schizobovine/pidplate/hardware/pidshield-mk-2.1.brd

## EAGLE design hardware/pidshield-mk-2.1.brd (2015-05-11)

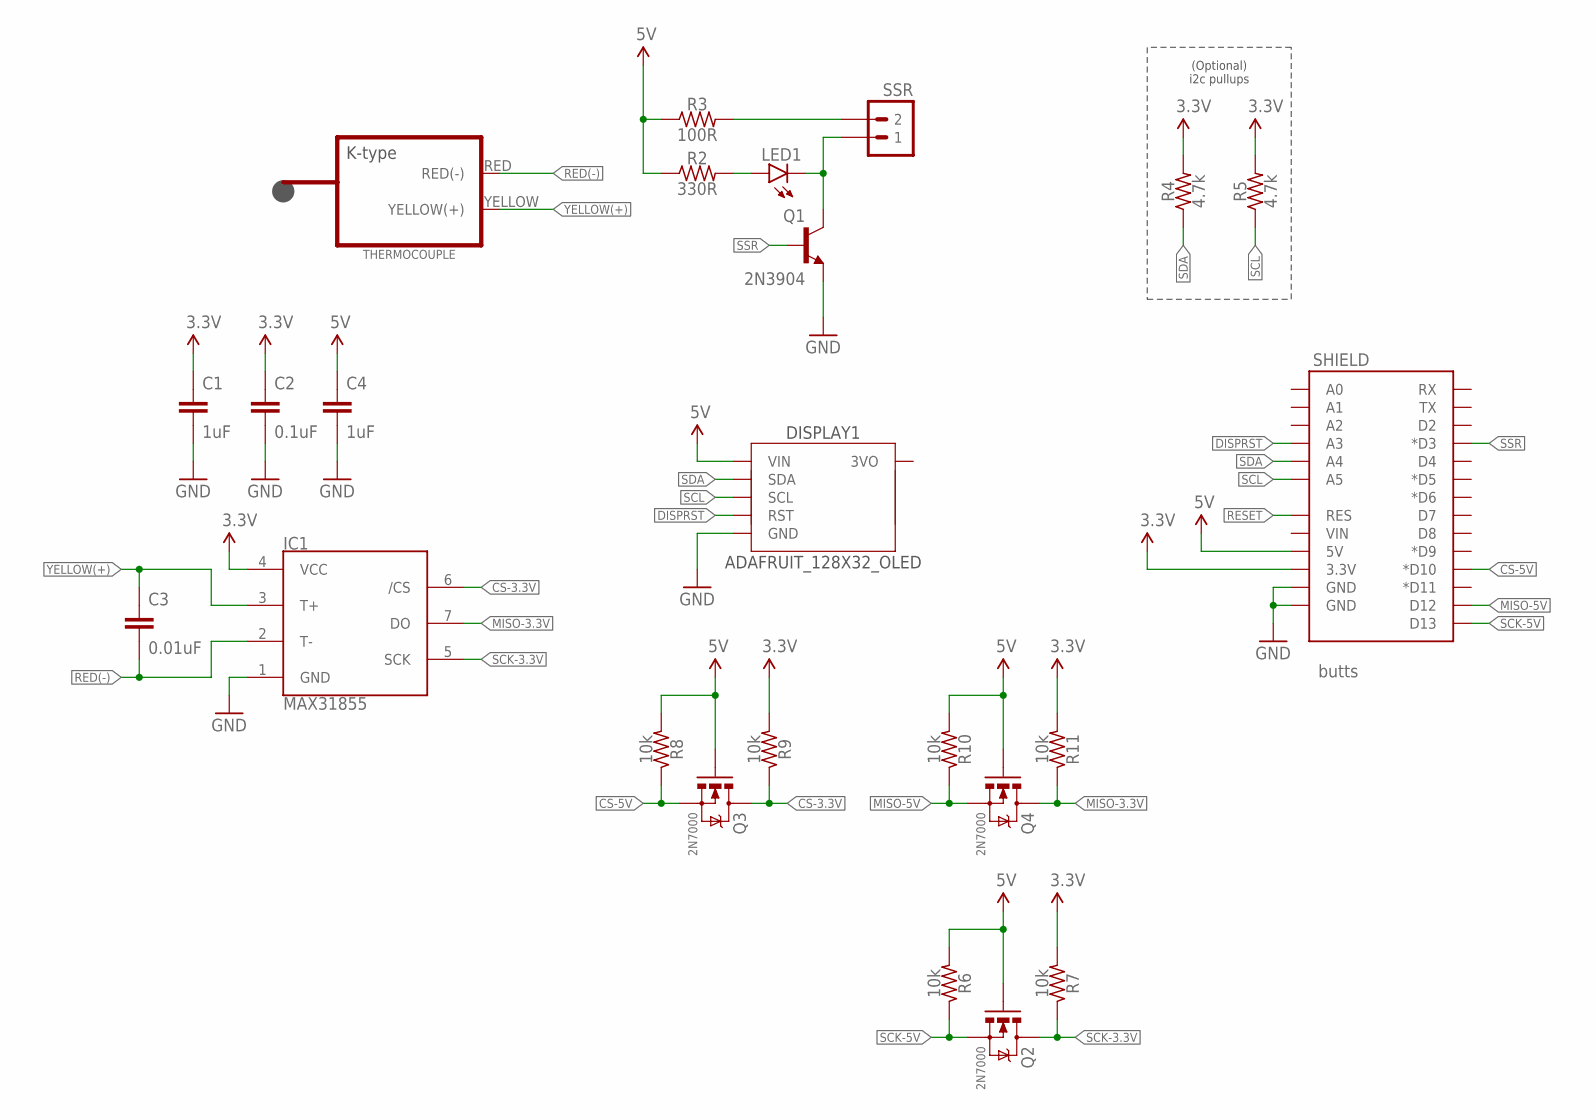
[picture p13: schematic pidshield-mk-2.1.sch]

Parts:
C1, C4: 1uF; C025-024X044
C2: 0.1uF; C025-024X044
C3: 0.01uF; C0805
DISPLAY1: ADAFRUIT_128X32_OLED; ADAFRUIT_128X32_OLED_I2C_CLOSER_NS
IC1: MAX31855; SOIC127P600X175-8N
LED1: LED3MM-LESS; LED3MM-LESSSILK
Q1: 2N3904; TO-92-AMMO
Q2, Q3, Q4: 2N7000; TO-92-AMMO
R2: 330R; RESISTOR-AXIAL-PTH-5.08MM
R3: 100R; RESISTOR-AXIAL-PTH-5.08MM
R4, R5: 4.7k; RESISTOR-AXIAL-PTH-5.08MM
R6, R7, R8, R9, R10, R11: 10k; RESISTOR-AXIAL-PTH-5.08MM
SHIELD: butts; ARDUINO_SHIELD_NOOUTLINE_INSIDE_SMALLER
SSR: M02JST-PTH-RA-SMALLPADS; JST-2-PH-RA-PTH-SMALLPADS
THERMOCOUPLE: THERMOCOUPLE-CONNECTORMINI-PCB; PCC-SMP

Connections:
3.3V: C1.1, C2.1, IC1.4 (VCC), R4.P$2 (2), R5.P$2 (2), R7.P$2 (2), R9.P$2 (2), R11.P$2 (2), SHIELD.3.3V
5V: C4.1, DISPLAY1.VIN, Q2.2 (G), Q3.2 (G), Q4.2 (G), R2.P$1 (1), R3.P$1 (1), R6.P$2 (2), R8.P$2 (2), R10.P$2 (2), SHIELD.5V
CS-3.3V: IC1.6 (/CS), Q3.3 (D), R9.P$1 (1)
CS-5V: Q3.1 (S), R8.P$1 (1), SHIELD.D10 (*D10)
DISPRST: DISPLAY1.RST, SHIELD.A3
GND: C1.2, C2.2, C4.2, DISPLAY1.GND, IC1.1 (GND), Q1.1 (E), SHIELD.GND@0 (GND), SHIELD.GND@1 (GND)
MISO-3.3V: IC1.7 (DO), Q4.3 (D), R11.P$1 (1)
MISO-5V: Q4.1 (S), R10.P$1 (1), SHIELD.D12
unnamed: LED1.A, R2.P$2 (2)
unnamed: LED1.K (C), Q1.3 (C), SSR.1
unnamed: R3.P$2 (2), SSR.2
RED(-): C3.2, IC1.2 (T-), THERMOCOUPLE.RED (RED(-))
RESET: SHIELD.RES
SCK-3.3V: IC1.5 (SCK), Q2.3 (D), R7.P$1 (1)
SCK-5V: Q2.1 (S), R6.P$1 (1), SHIELD.D13
SCL: DISPLAY1.SCL, R5.P$1 (1), SHIELD.A5
SDA: DISPLAY1.SDA, R4.P$1 (1), SHIELD.A4
SSR: Q1.2 (B), SHIELD.D3 (*D3)
YELLOW(+): C3.1, IC1.3 (T+), THERMOCOUPLE.YELLOW (YELLOW(+))

Notes on the sheet:
(Optional) i2c pullups

Board: 2 copper layers, 30 parts (2 on the bottom side), 18 nets, no tracks yet.

Other parts of the board:
U$2: COW
U$3: COW_SMALL
U$4, U$5: CC-BY-SA-4.0-NO-URL
U$6: OSHWLOGO_TOP_0.2_A
U$7: OSHWLOGO_BOT_0.2_A
