schizobovine/pidplate/hardware/pidshield-mk-2.brd

## EAGLE design hardware/pidshield-mk-2.brd (2014-12-28)

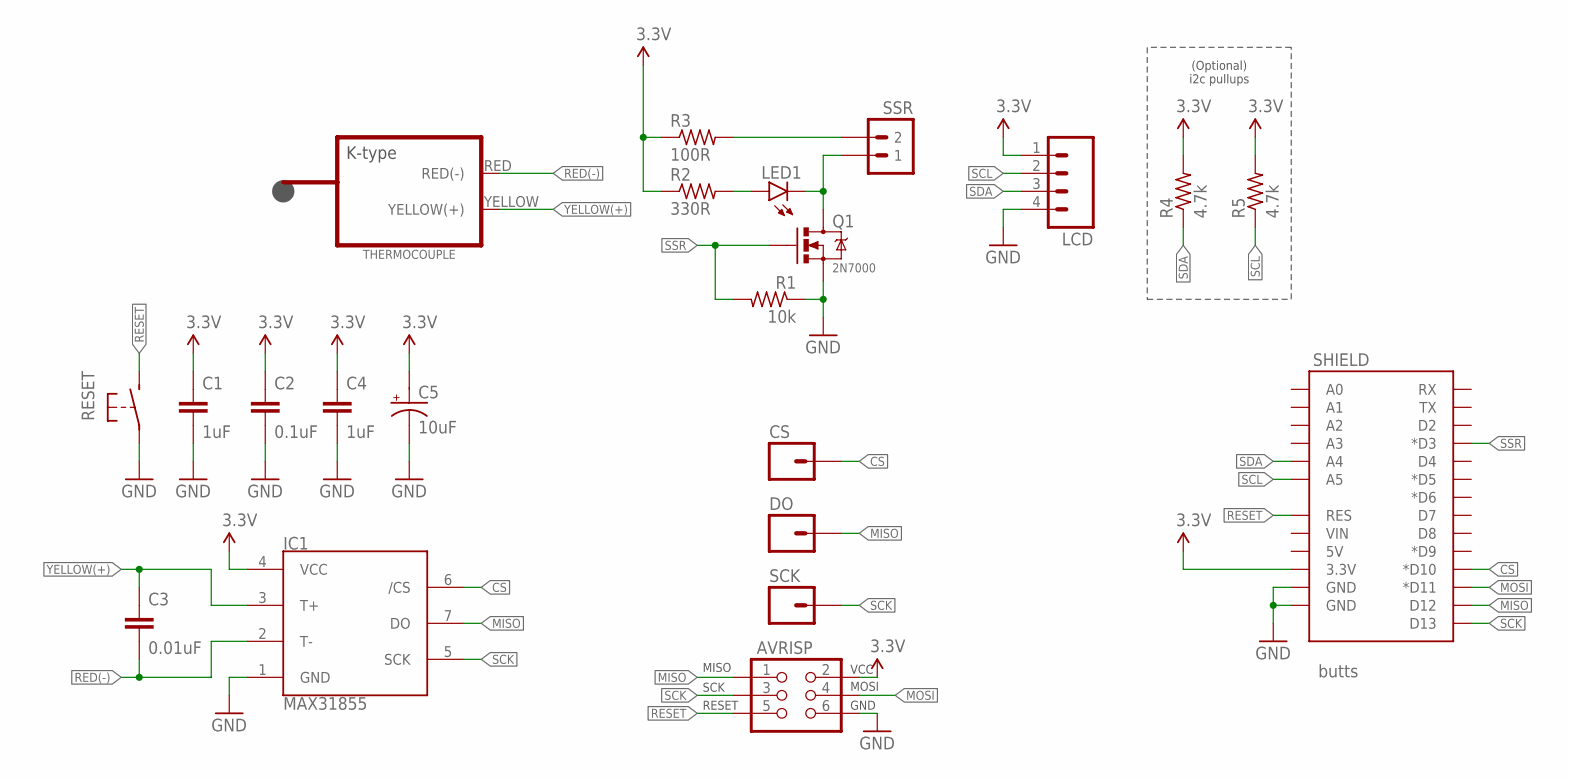
[picture p14: schematic pidshield-mk-2.sch]

Parts:
AVRISP: AVR_SPI_PRG_6PTH; 2X3
C1, C4: 1uF; C025-024X044
C2: 0.1uF; C025-024X044
C3: 0.01uF; C025-024X044
C5: 10uF; E2-5
CS: M01PTH; 1X01
DO: M01PTH; 1X01
IC1: MAX31855; SOIC127P600X175-8N
LCD: M04JST_XH_RA; JST-4-XH-RA-PTH
LED1: LED3MM
Q1: 2N7000; TO-92-AMMO
R1: 10k; RESISTOR-AXIAL-PTH-6.35MM
R2: 330R; RESISTOR-AXIAL-PTH-6.35MM
R3: 100R; RESISTOR-AXIAL-PTH-6.35MM
R4, R5: 4.7k; RESISTOR-AXIAL-PTH-6.35MM
RESET: SPST-NO-TACT6MM-PTH-SMALL-PADS; DTS-6-SMALL-PADS
SCK: M01PTH; 1X01
SHIELD: butts; ARDUINO_SHIELD_NOOUTLINE_INSIDE_SMALLER
SSR: M02JST-PTH-RA-SMALLPADS; JST-2-PH-RA-PTH-SMALLPADS
THERMOCOUPLE: THERMOCOUPLE-CONNECTORMINI-PCB; PCC-SMP

Connections:
3.3V: AVRISP.2 (VCC), C1.1, C2.1, C4.1, C5.+, IC1.4 (VCC), LCD.1, R2.P$1 (1), R3.P$1 (1), R4.P$2 (2), R5.P$2 (2), SHIELD.3.3V
CS: CS.1, IC1.6 (/CS), SHIELD.D10 (*D10)
GND: AVRISP.6 (GND), C1.2, C2.2, C4.2, C5.-, IC1.1 (GND), LCD.4, Q1.1 (S), R1.P$1 (1), RESET.1, RESET.2 (1), SHIELD.GND@0 (GND), SHIELD.GND@1 (GND)
MISO: AVRISP.1 (MISO), DO.1, IC1.7 (DO), SHIELD.D12
MOSI: AVRISP.4 (MOSI), SHIELD.D11 (*D11)
unnamed: LED1.A, R2.P$2 (2)
unnamed: LED1.K (C), Q1.3 (D), SSR.1
unnamed: R3.P$2 (2), SSR.2
RED(-): C3.2, IC1.2 (T-), THERMOCOUPLE.RED (RED(-))
RESET: AVRISP.5 (RESET), RESET.3 (2), RESET.4 (2), SHIELD.RES
SCK: AVRISP.3 (SCK), IC1.5 (SCK), SCK.1, SHIELD.D13
SCL: LCD.2, R5.P$1 (1), SHIELD.A5
SDA: LCD.3, R4.P$1 (1), SHIELD.A4
SSR: Q1.2 (G), R1.P$2 (2), SHIELD.D3 (*D3)
YELLOW(+): C3.1, IC1.3 (T+), THERMOCOUPLE.YELLOW (YELLOW(+))

Notes on the sheet:
(Optional) i2c pullups
