schizobovine/pidplate/hardware/pidshield-mk-2.brd

## EAGLE design hardware/pidshield-mk-2.brd (continued)

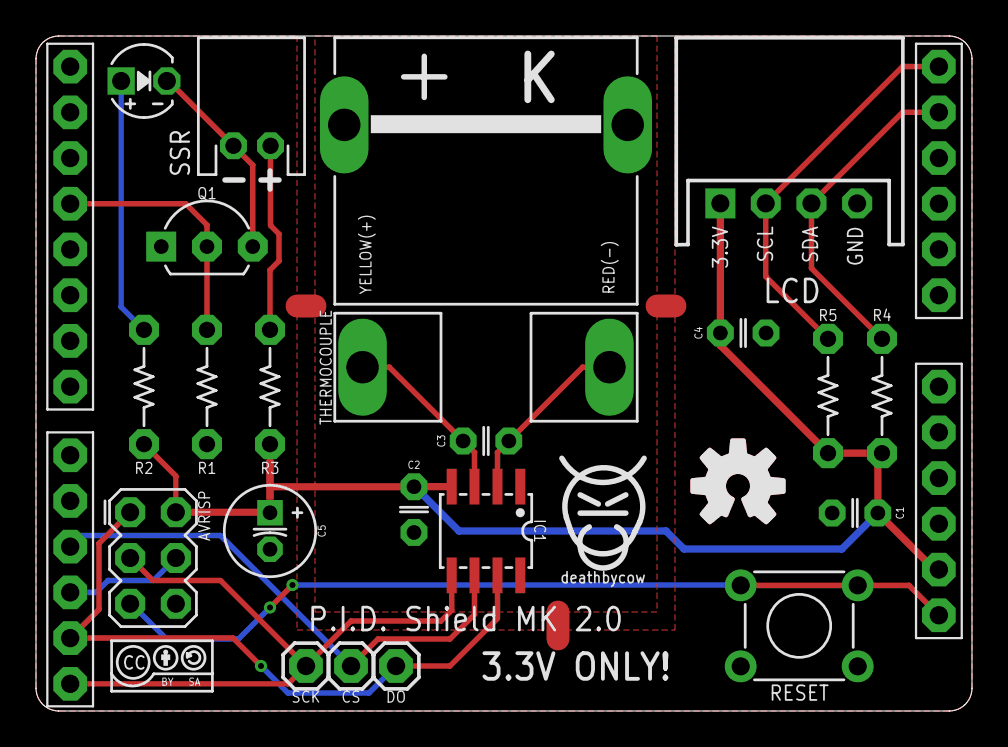
[picture p15: board pidshield-mk-2.brd from above]

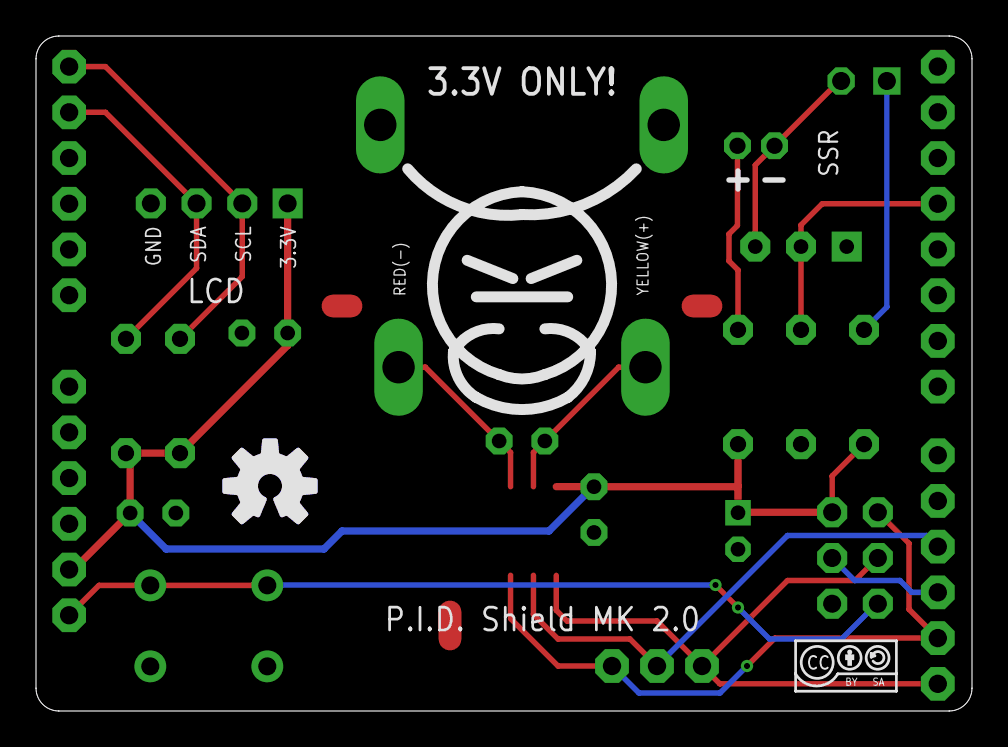
[picture p16: board pidshield-mk-2.brd from below]

Board: 2 copper layers, 52.0 x 37.5 mm, 28 parts (2 on the bottom side), 15 nets.

Other parts of the board:
U$2: COW
U$3: COW_SMALL
U$4, U$5: CC-BY-SA-4.0-NO-URL
U$6: OSHWLOGO_TOP_0.2_A
U$7: OSHWLOGO_BOT_0.2_A
