schizobovine/pidplate/hardware/pidshield-mk-1.brd

## EAGLE design hardware/pidshield-mk-1.brd (2014-12-15)

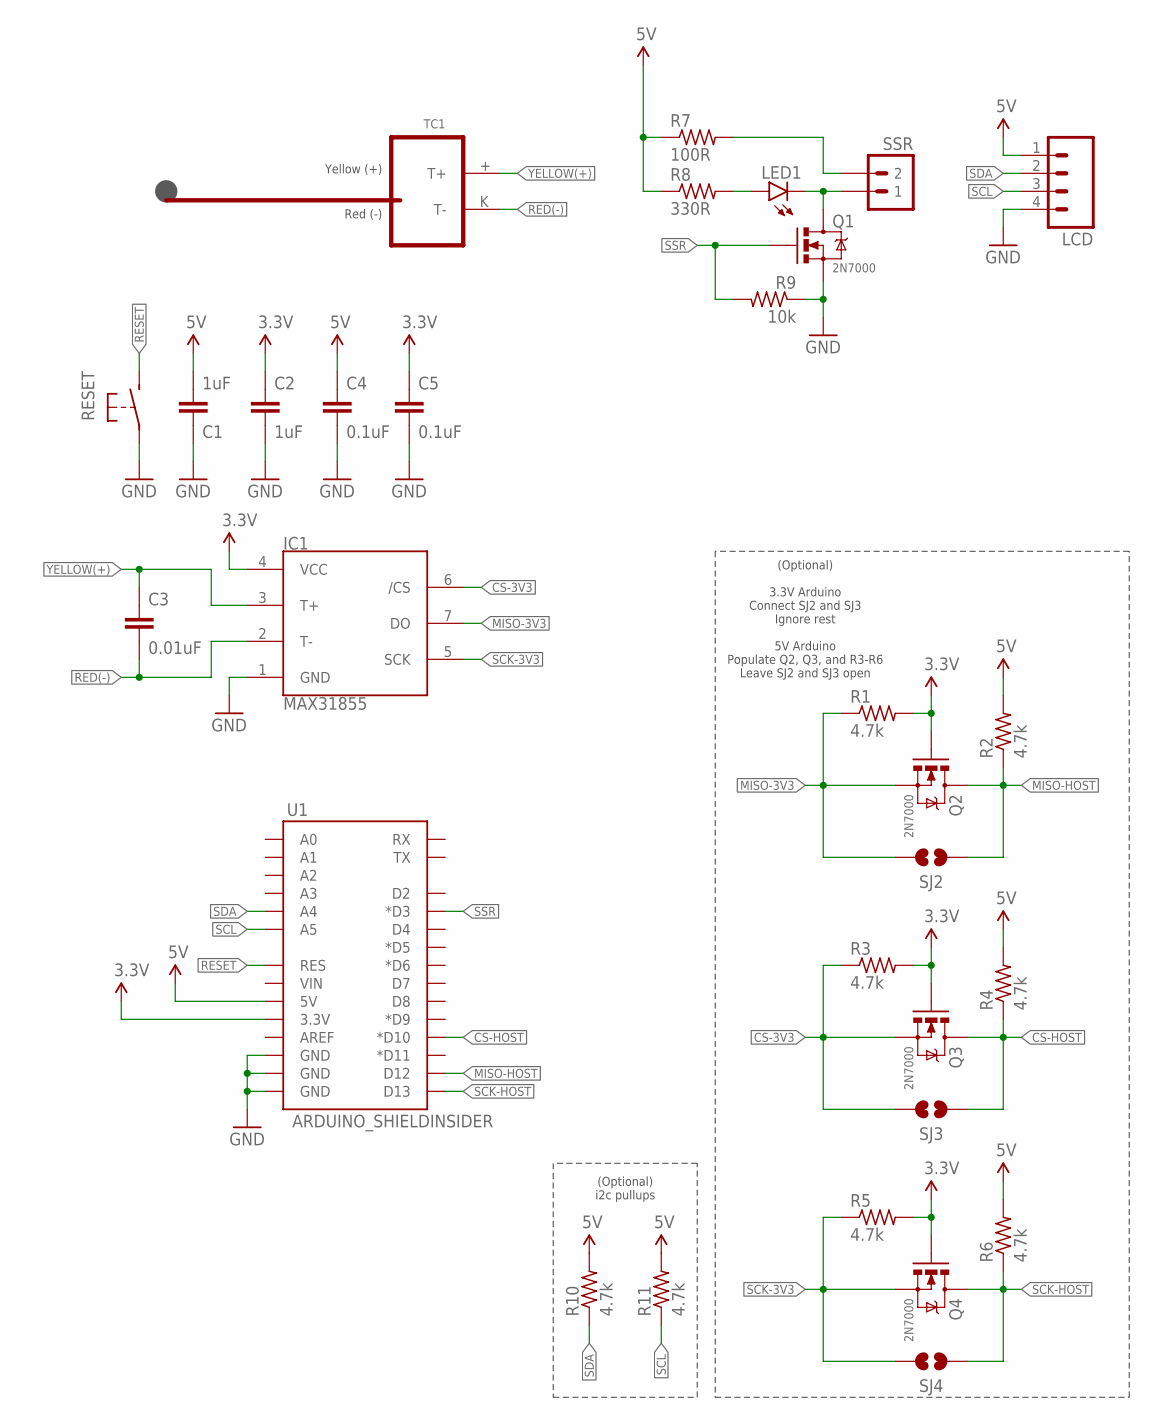
[picture p17: schematic pidshield-mk-1.sch]

Parts:
C1, C2: 1uF; C025-024X044
C3: 0.01uF; C025-024X044
C4, C5: 0.1uF; C025-024X044
IC1: MAX31855; SOIC127P600X175-8N
LCD: M04JST_XH_RA; JST-4-XH-RA-PTH
LED1: LED3MM
Q1, Q2, Q3, Q4: 2N7000; TO-92-AMMO
R1, R2, R3, R4, R5, R6, R10, R11: 4.7k; RESISTOR-AXIAL-PTH-6.35MM
R7: 100R; RESISTOR-AXIAL-PTH-6.35MM
R8: 330R; RESISTOR-AXIAL-PTH-6.35MM
R9: 10k; RESISTOR-AXIAL-PTH-6.35MM
RESET: SPST-NO-TACT3MM-RA; TACTILE-PTH-SIDE
SJ2, SJ3, SJ4: JUMPER-PAD-2-NOYES_SILK; PAD-JUMPER-2-NO_YES_SILK
SSR: M02JST-PTH-RA-SMALLPADS; JST-2-PH-RA-PTH-SMALLPADS
TC1: PCC-SMP-K; PCC-SMP
U1: ARDUINO_SHIELDINSIDER; ARDUINO_SHIELD_NOOUTLINE_INSIDE

Connections:
3.3V: C2.1, C5.1, IC1.4 (VCC), Q2.2 (G), Q3.2 (G), Q4.2 (G), R1.P$2 (2), R3.P$2 (2), R5.P$2 (2), U1.3.3V
5V: C1.2, C4.1, LCD.1, R2.P$2 (2), R4.P$2 (2), R6.P$2 (2), R7.P$1 (1), R8.P$1 (1), R10.P$2 (2), R11.P$2 (2), U1.5V
CS-3V3: IC1.6 (/CS), Q3.1 (S), R3.P$1 (1), SJ3.2
CS-HOST: Q3.3 (D), R4.P$1 (1), SJ3.1, U1.D10 (*D10)
GND: C1.1, C2.2, C4.2, C5.2, IC1.1 (GND), LCD.4, Q1.1 (S), R9.P$1 (1), RESET.1, U1.GND@0 (GND), U1.GND@1 (GND), U1.GND@2 (GND)
MISO-3V3: IC1.7 (DO), Q2.1 (S), R1.P$1 (1), SJ2.2
MISO-HOST: Q2.3 (D), R2.P$1 (1), SJ2.1, U1.D12
unnamed: LED1.A, R8.P$2 (2)
unnamed: LED1.K (C), Q1.3 (D), SSR.1
unnamed: R7.P$2 (2), SSR.2
RED(-): C3.2, IC1.2 (T-), TC1.K (T-)
RESET: RESET.2, U1.RES
SCK-3V3: IC1.5 (SCK), Q4.1 (S), R5.P$1 (1), SJ4.2
SCK-HOST: Q4.3 (D), R6.P$1 (1), SJ4.1, U1.D13
SCL: LCD.3, R11.P$1 (1), U1.A5
SDA: LCD.2, R10.P$1 (1), U1.A4
SSR: Q1.2 (G), R9.P$2 (2), U1.D3 (*D3)
YELLOW(+): C3.1, IC1.3 (T+), TC1.+ (T+)

Notes on the sheet:
(Optional) 3.3V Arduino Connect SJ2 and SJ3 Ignore rest 5V Arduino Populate Q2, Q3, and R3-R6 Leave SJ2 and SJ3 open
(Optional) i2c pullups

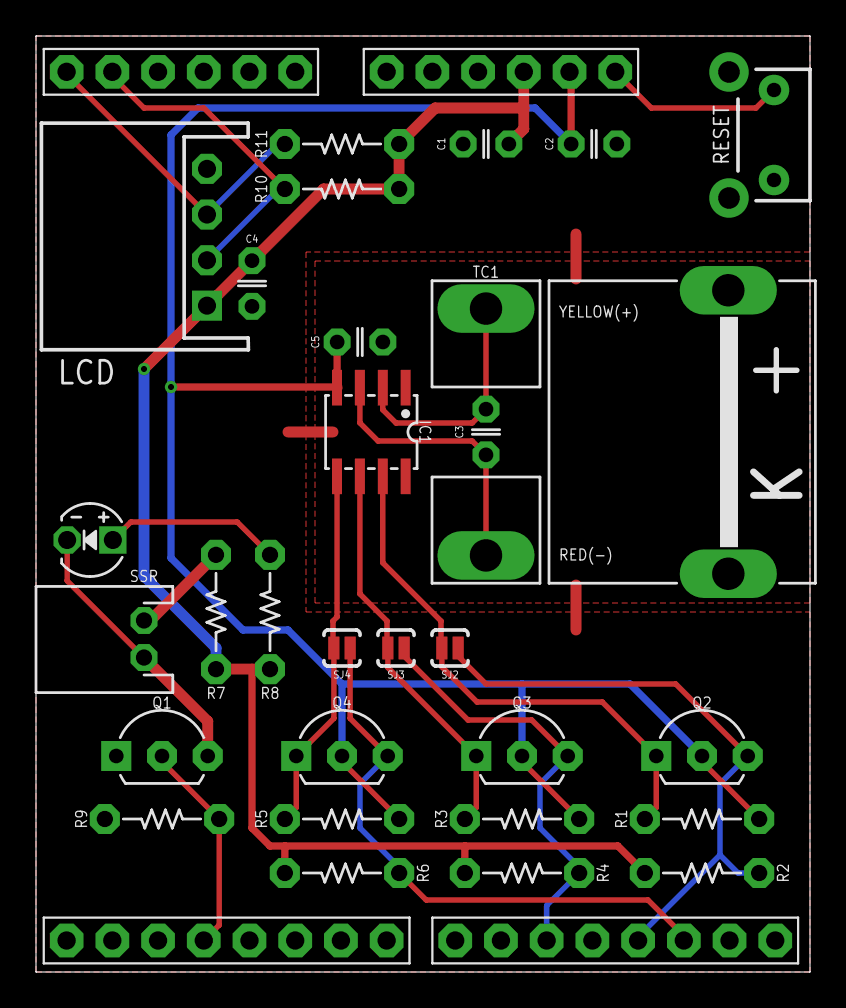
[picture p18: board pidshield-mk-1.brd from above]

Board: 2 copper layers, 43.0 x 52.0 mm, 30 parts (0 on the bottom side), 18 nets.
