schizobovine/pidplate/hardware/pidplate-mk-2.1.brd

## EAGLE design hardware/pidplate-mk-2.1.brd (2014-12-15)

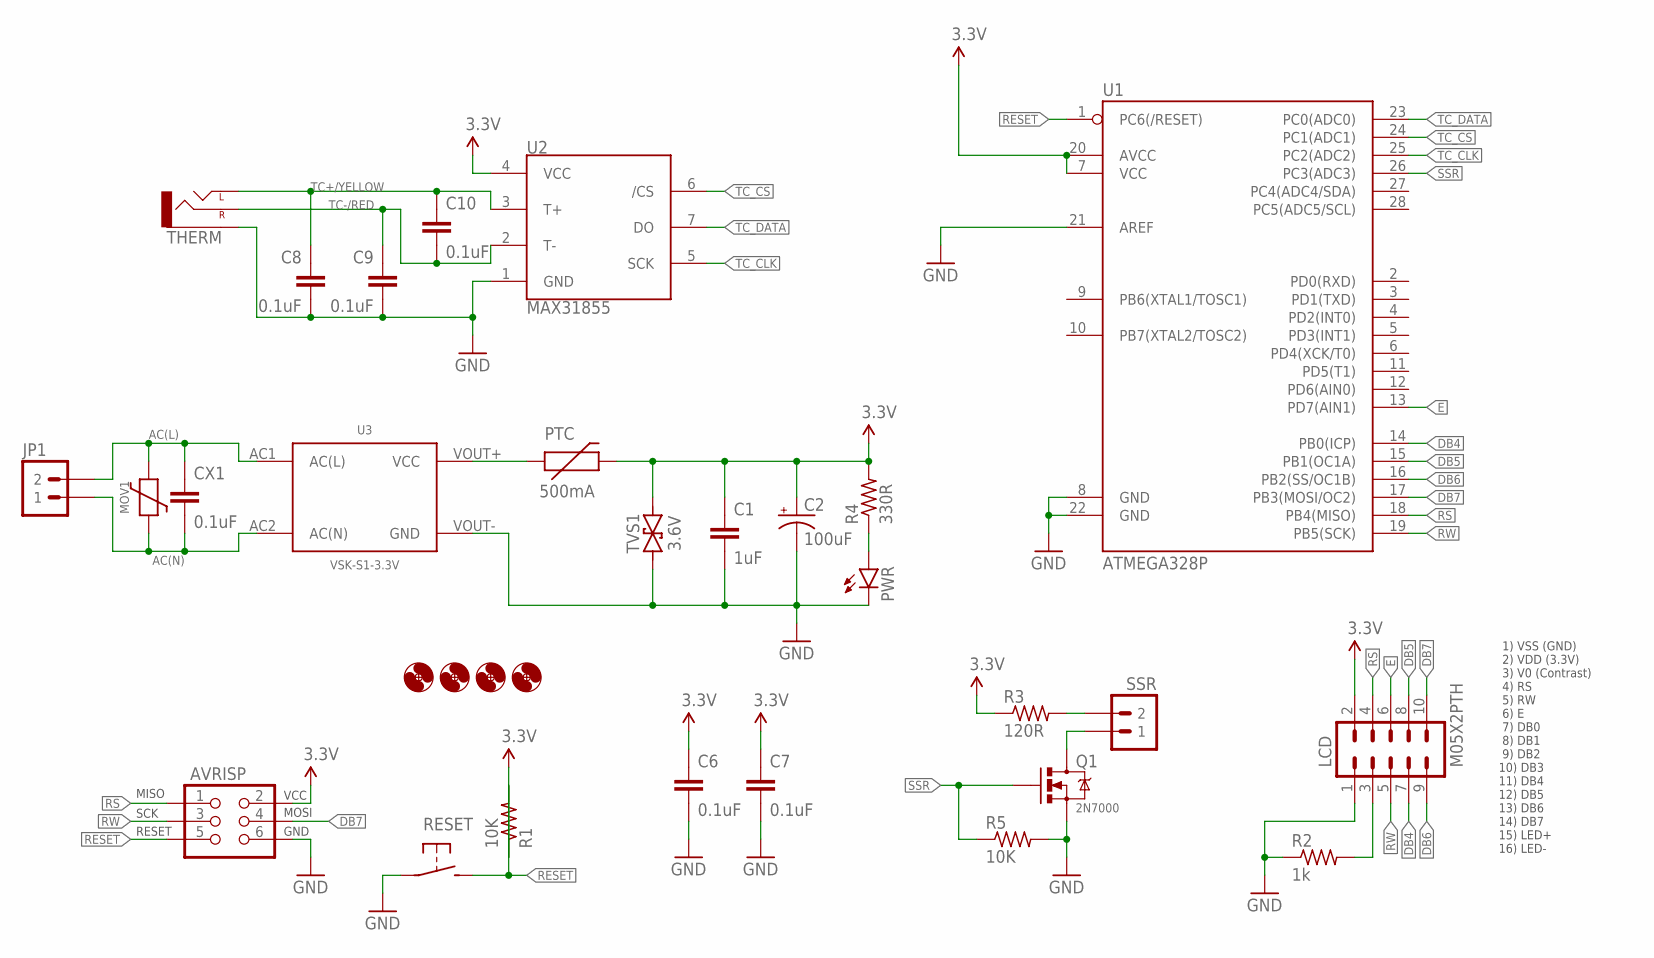
[picture p19: schematic pidplate-mk-2.1.sch]

Parts:
AVRISP: AVR_SPI_PRG_6PTH; 2X3
C1: 1uF; C025-024X044
C2: 100uF; E2,5-7
C6, C7, C8, C9, C10: 0.1uF; C025-024X044
CX1: 0.1uF; XC10B5
H1, H2, H3, H4: HOLE#2; HOLE-#2
JP1: M023.5MM; SCREWTERMINAL-3.5MM-2
LCD: M05X2PTH; AVR_ICSP
MOV1: VARISITORVAR-5.08MM-PTH; VAR-5.08MM-PTH
PTC: 500mA; PTC
PWR: LED3MM
Q1: 2N7000; TO-92-AMMO
R1, R5: 10K; RESISTOR-AXIAL-PTH-6.35MM
R2: 1k; RESISTOR-AXIAL-PTH-6.35MM
R3: 120R; RESISTOR-AXIAL-PTH-6.35MM
R4: 330R; RESISTOR-AXIAL-PTH-6.35MM
RESET: SPST-NO-TACT3MM-PTH-SMALL-PADS; DTS-3-SMALL-PADS
SSR: M02JST-PTH-VERT; JST-2-PH-VERT-PTH
THERM: AUDIO-JACK2.5MM; STEREOJACK2.5MM_STEREOJACK2.5MM
TVS1: 3.6V; DO-41-TVS
U1: ATMEGA328P; DIL28-3
U2: MAX31855; SOIC127P600X175-8N
U3: VSK-S1-3.3V; VSK-S1

Connections:
3.3V: AVRISP.2 (VCC), C1.1, C2.+, C6.1, C7.1, LCD.2, PTC.P$2 (2), R1.P$1 (1), R3.P$1 (1), R4.P$2 (2), TVS1.P$2 (2), U1.7 (VCC), U1.20 (AVCC), U2.4 (VCC)
AC(L): CX1.1, JP1.2, MOV1.2, U3.AC1 (AC(L))
AC(N): CX1.2, JP1.1, MOV1.1, U3.AC2 (AC(N))
DB4: LCD.7, U1.14 (PB0(ICP))
DB5: LCD.8, U1.15 (PB1(OC1A))
DB6: LCD.9, U1.16 (PB2(SS/OC1B))
DB7: AVRISP.4 (MOSI), LCD.10, U1.17 (PB3(MOSI/OC2))
E: LCD.6, U1.13 (PD7(AIN1))
GND: AVRISP.6 (GND), C1.2, C2.-, C6.2, C7.2, C8.2, C9.2, LCD.1, PWR.K (C), Q1.1 (S), R2.P$1 (1), R5.P$2 (2), RESET.1, THERM.SHIELD (SLEEVE), TVS1.P$1 (1), U1.8 (GND), U1.21 (AREF), U1.22 (GND), U2.1 (GND), U3.VOUT- (GND)
unnamed: PTC.P$1 (1), U3.VOUT+ (VCC)
unnamed: LCD.3, R2.P$2 (2)
unnamed: R3.P$2 (2), SSR.2
unnamed: Q1.3 (D), SSR.1
unnamed: PWR.A, R4.P$1 (1)
RESET: AVRISP.5 (RESET), R1.P$2 (2), RESET.2, U1.1 (PC6(/RESET))
RS: AVRISP.1 (MISO), LCD.4, U1.18 (PB4(MISO))
RW: AVRISP.3 (SCK), LCD.5, U1.19 (PB5(SCK))
SSR: Q1.2 (G), R5.P$1 (1), U1.26 (PC3(ADC3))
TC+/YELLOW: C8.1, C10.1, THERM.RING1 (LEFT), THERM.RING2 (LEFT), U2.3 (T+)
TC-/RED: C9.1, C10.2, THERM.TIP (RIGHT), U2.2 (T-)
TC_CLK: U1.25 (PC2(ADC2)), U2.5 (SCK)
TC_CS: U1.24 (PC1(ADC1)), U2.6 (/CS)
TC_DATA: U1.23 (PC0(ADC0)), U2.7 (DO)

Notes on the sheet:
1) VSS (GND) 2) VDD (3.3V) 3) V0 (Contrast) 4) RS 5) RW 6) E 7) DB0 8) DB1 9) DB2 10) DB3 11) DB4 12) DB5 13) DB6 14) DB7 15) LED+ 16) LED-

Board: 2 copper layers, 35 parts (2 on the bottom side), 23 nets, no tracks yet.

Other parts of the board:
U$1, U$4: OSHWLOGO_BOT_0.2
U$2, U$3: CC-BY-SA-4.0-NO-URL
