schizobovine/pidplate/hardware/pidplate-mk-2.brd

## EAGLE design hardware/pidplate-mk-2.brd (2014-12-11)

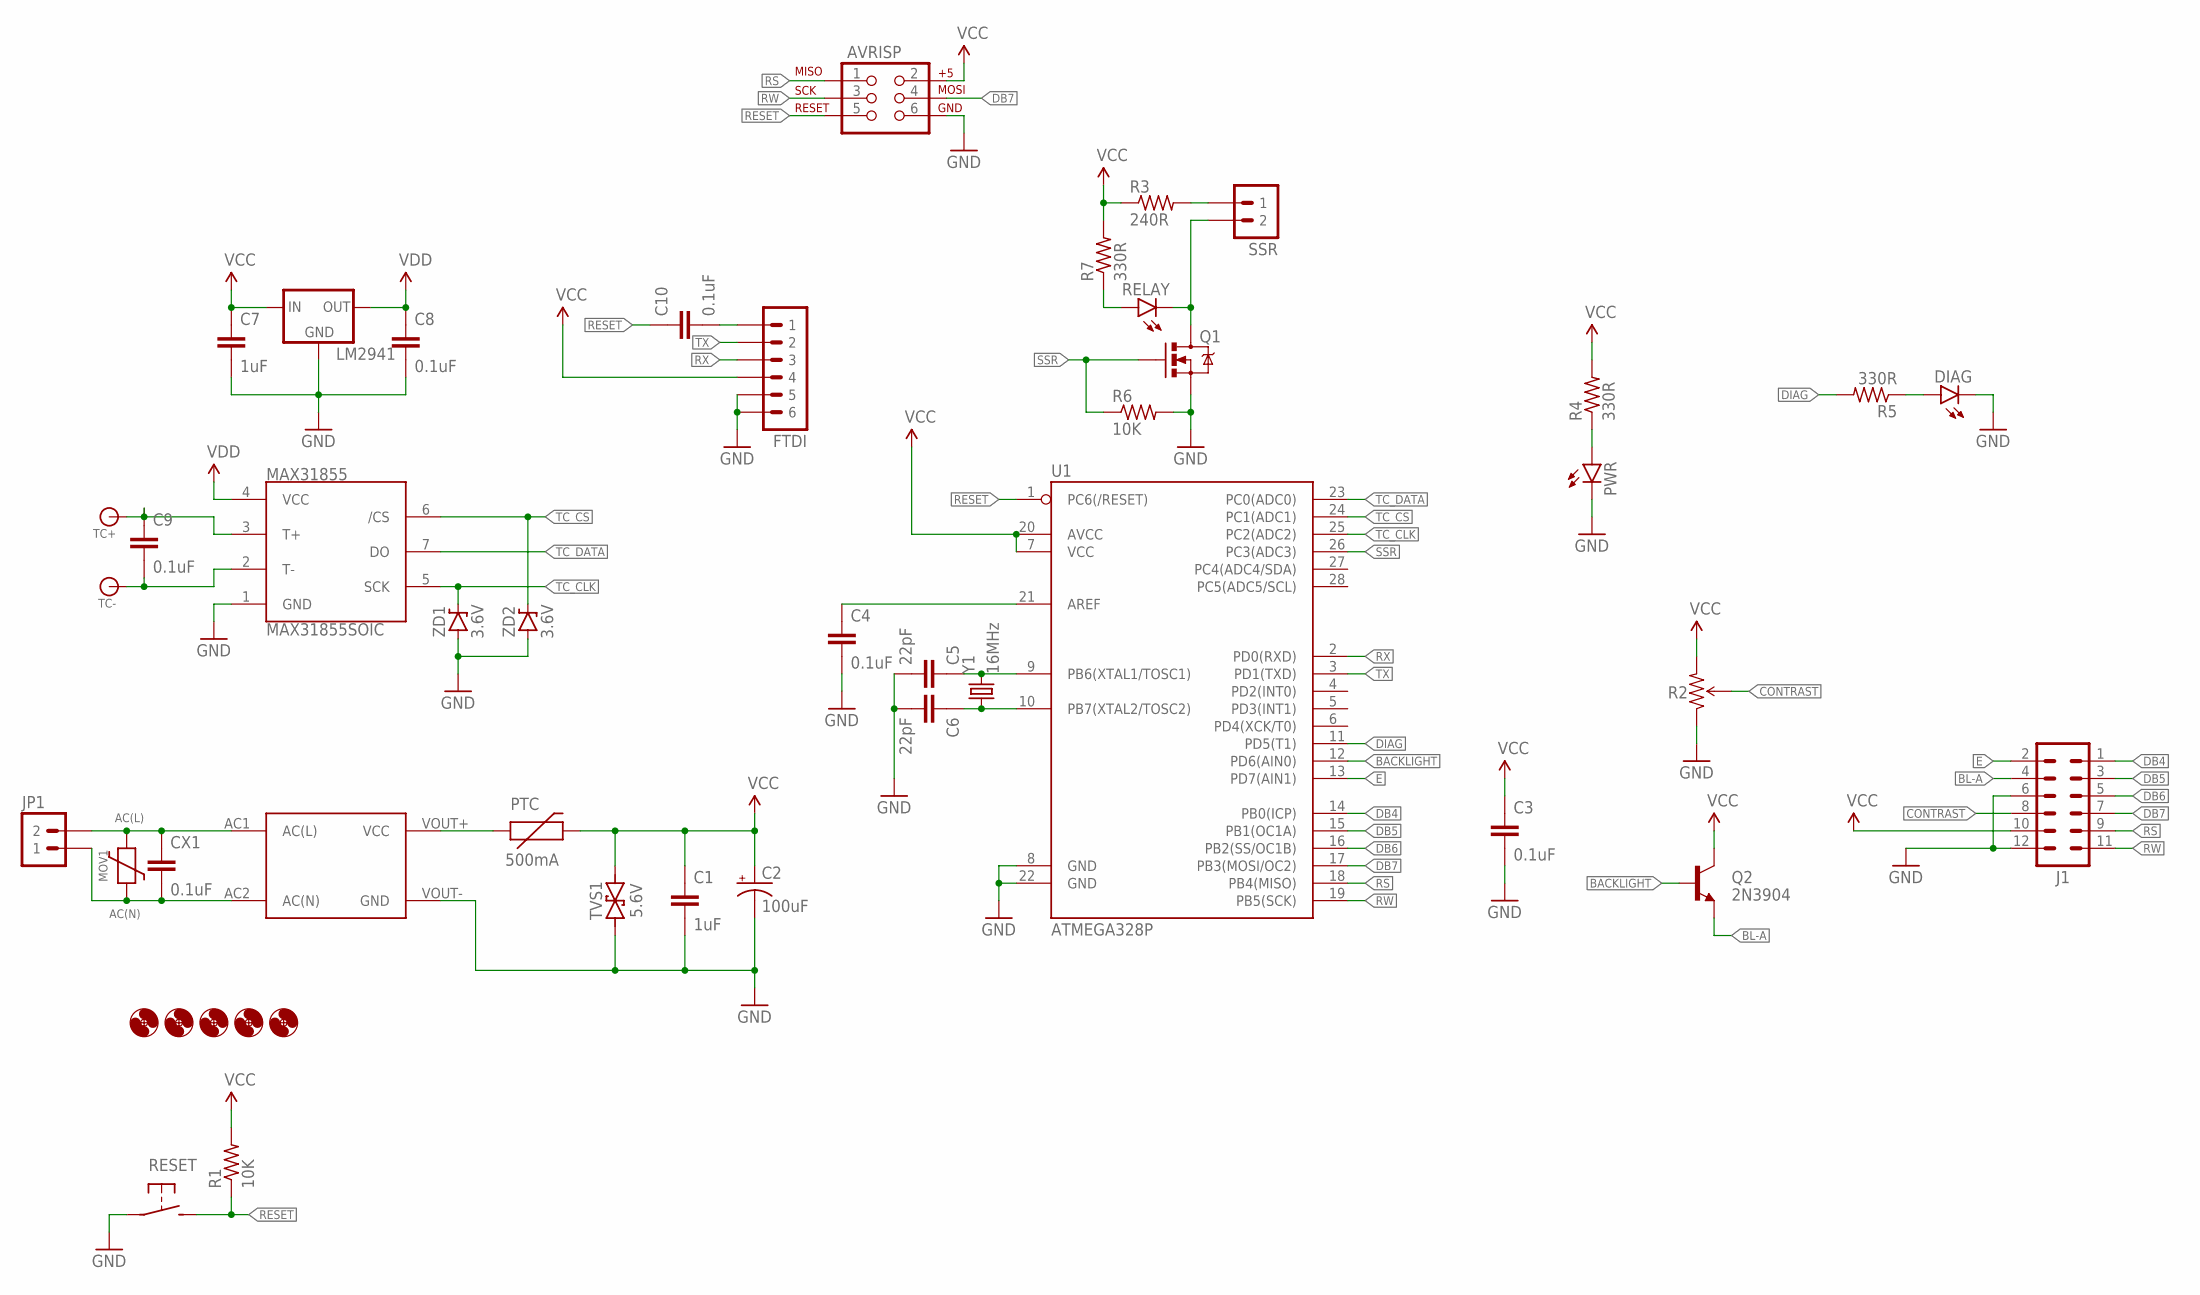
[picture p20: schematic pidplate-mk-2.sch]

Parts:
AVRISP: AVR_SPI_PRG_6PTH; 2X3
C1, C7: 1uF; C025-024X044
C2: 100uF; E2,5-7
C3, C4, C8, C9, C10: 0.1uF; C025-024X044
C5, C6: 22pF; C025-024X044
CX1: 0.1uF; XC10B5
DIAG: LED3MM
FTDI: M06SIP; 1X06
H1, H2, H3, H4, H5: HOLE#2; HOLE-#2
J1: M06X2PTH; 2X6_PTH
JP1: M023.5MM; SCREWTERMINAL-3.5MM-2
LM2941: L2941; TO-92-AMMO
MAX31855: MAX31855SOIC; SOIC127P600X175-8N
MOV1: VARISITORVAR-5.08MM-PTH; VAR-5.08MM-PTH
PTC: 500mA; PTC
PWR: LED3MM
Q1: 2N7000; TO-92-AMMO
Q2: 2N3904; TO-92-AMMO
R1: 10K; RESISTOR-AXIAL-PTH-5.08MM
R2: 20K; TRIM_POT_PTH
R3: 240R; RESISTOR-AXIAL-PTH-6.35MM
R4, R5, R7: 330R; RESISTOR-AXIAL-PTH-5.08MM
R6: 10K; RESISTOR-AXIAL-PTH-6.35MM
RELAY: LED3MM
RESET: SPST-NO-TACT3MM-RA; TACTILE-PTH-SIDE
SSR: M02JST-PTH-VERT; JST-2-PH-VERT-PTH
TC+: BANANA_CONNPTH-RA; BANANA-PTH-RA-SAFEWORD
TC-: BANANA_CONNPTH-RA; BANANA-PTH-RA-SAFEWORD
TVS1: 5.6V; DO-41-TVS
U1: ATMEGA328P; DIL28-3
U3: VSK-S1
Y1: 16MHz; HC49U-V
ZD1, ZD2: 3.6V; DIODE-7.68MM

Connections:
AC(L): CX1.1, JP1.2, MOV1.2, U3.AC1 (AC(L))
AC(N): CX1.2, JP1.1, MOV1.1, U3.AC2 (AC(N))
BACKLIGHT: Q2.2 (B), U1.12 (PD6(AIN0))
BL-A: J1.4, Q2.3 (E)
CONTRAST: J1.8, R2.2 (WIPER)
DB4: J1.1, U1.14 (PB0(ICP))
DB5: J1.3, U1.15 (PB1(OC1A))
DB6: J1.5, U1.16 (PB2(SS/OC1B))
DB7: AVRISP.4, J1.7, U1.17 (PB3(MOSI/OC2))
DIAG: R5.P$2 (2), U1.11 (PD5(T1))
E: J1.2, U1.13 (PD7(AIN1))
GND: AVRISP.6, C1.2, C2.-, C3.2, C4.2, C5.2, C6.2, C7.2, C8.2, DIAG.K (C), FTDI.5, FTDI.6, J1.6, J1.12, LM2941.2 (GND), MAX31855.1 (GND), PWR.K (C), Q1.1 (S), R2.1 (CCW), R6.P$2 (2), RESET.1, TVS1.P$1 (1), U1.8 (GND), U1.22 (GND), U3.VOUT- (GND), ZD1.A, ZD2.A
unnamed: PTC.P$1 (1), U3.VOUT+ (VCC)
unnamed: DIAG.A, R5.P$1 (1)
unnamed: C6.1, U1.10 (PB7(XTAL2/TOSC2)), Y1.1
unnamed: C5.1, U1.9 (PB6(XTAL1/TOSC1)), Y1.2
unnamed: C4.1, U1.21 (AREF)
unnamed: R3.P$2 (2), SSR.1
unnamed: C9.2, MAX31855.2 (T-), TC-.P$1, TC-.P$2
unnamed: C9.1, MAX31855.3 (T+), TC+.P$1, TC+.P$2
unnamed: Q1.3 (D), RELAY.K (C), SSR.2
unnamed: PWR.A, R4.P$1 (1)
unnamed: R7.P$1 (1), RELAY.A
unnamed: C10.2, FTDI.1
RESET: AVRISP.5, C10.1, R1.P$1 (1), RESET.2, U1.1 (PC6(/RESET))
RS: AVRISP.1, J1.9, U1.18 (PB4(MISO))
RW: AVRISP.3, J1.11, U1.19 (PB5(SCK))
RX: FTDI.3, U1.2 (PD0(RXD))
SSR: Q1.2 (G), R6.P$1 (1), U1.26 (PC3(ADC3))
TC_CLK: MAX31855.5 (SCK), U1.25 (PC2(ADC2)), ZD1.K (C)
TC_CS: MAX31855.6 (/CS), U1.24 (PC1(ADC1)), ZD2.K (C)
TC_DATA: MAX31855.7 (DO), U1.23 (PC0(ADC0))
TX: FTDI.2, U1.3 (PD1(TXD))
VCC: AVRISP.2, C1.1, C2.+, C3.1, C7.1, FTDI.4, J1.10, LM2941.1 (IN), PTC.P$2 (2), Q2.1 (C), R1.P$2 (2), R2.3 (CW), R3.P$1 (1), R4.P$2 (2), R7.P$2 (2), TVS1.P$2 (2), U1.7 (VCC), U1.20 (AVCC)
VDD: C8.1, LM2941.3 (OUT), MAX31855.4 (VCC)

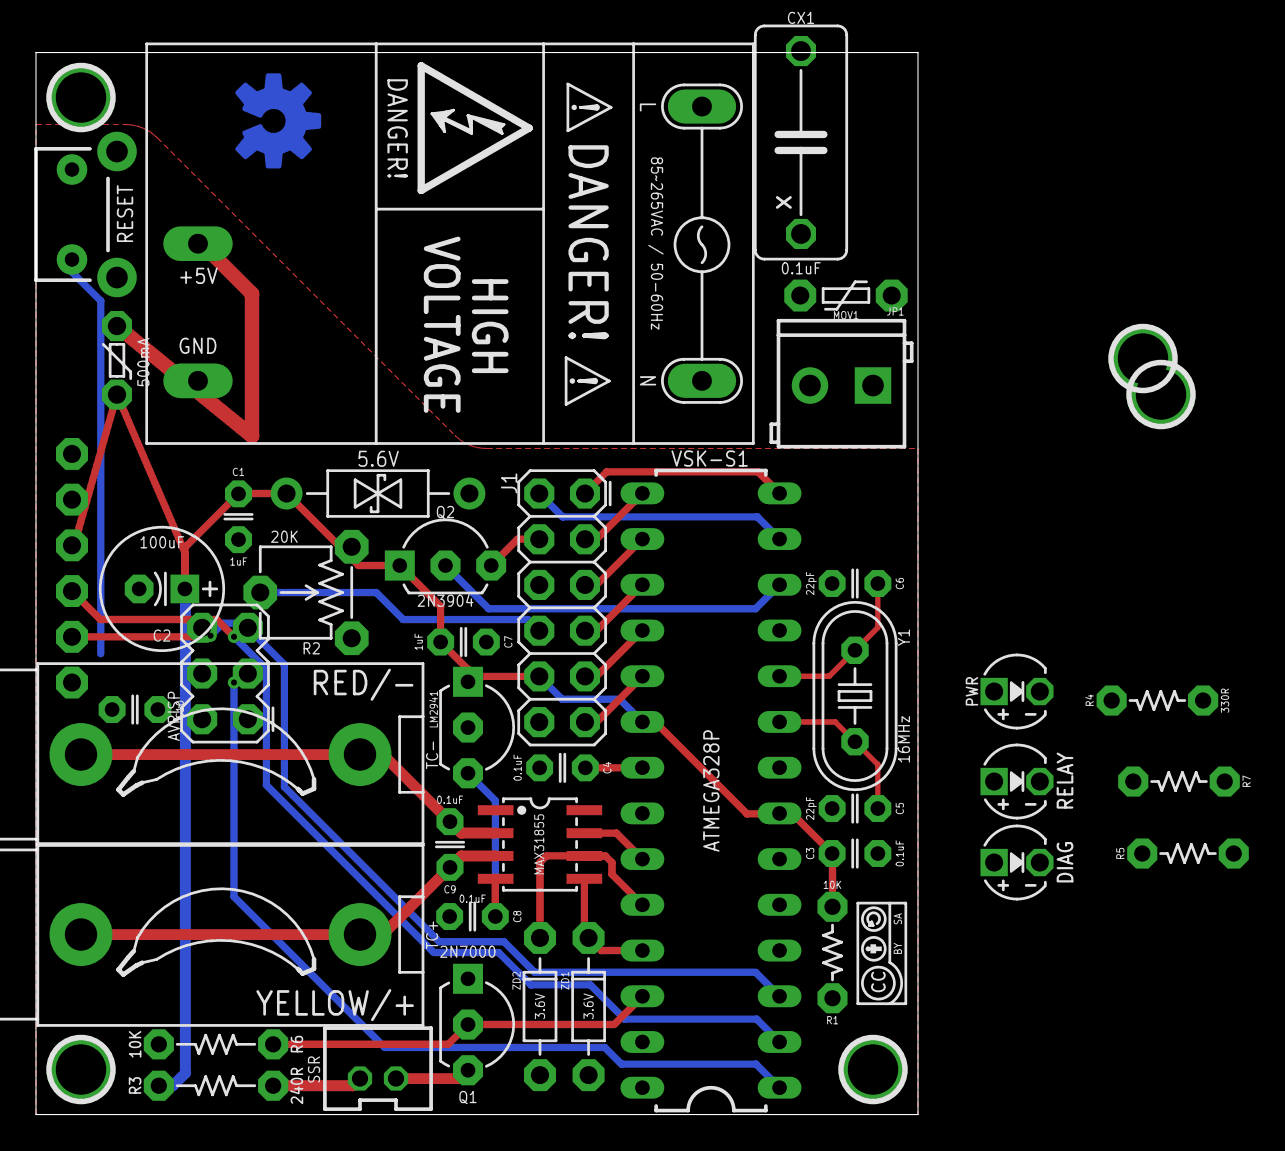
[picture p21: board pidplate-mk-2.brd from above]

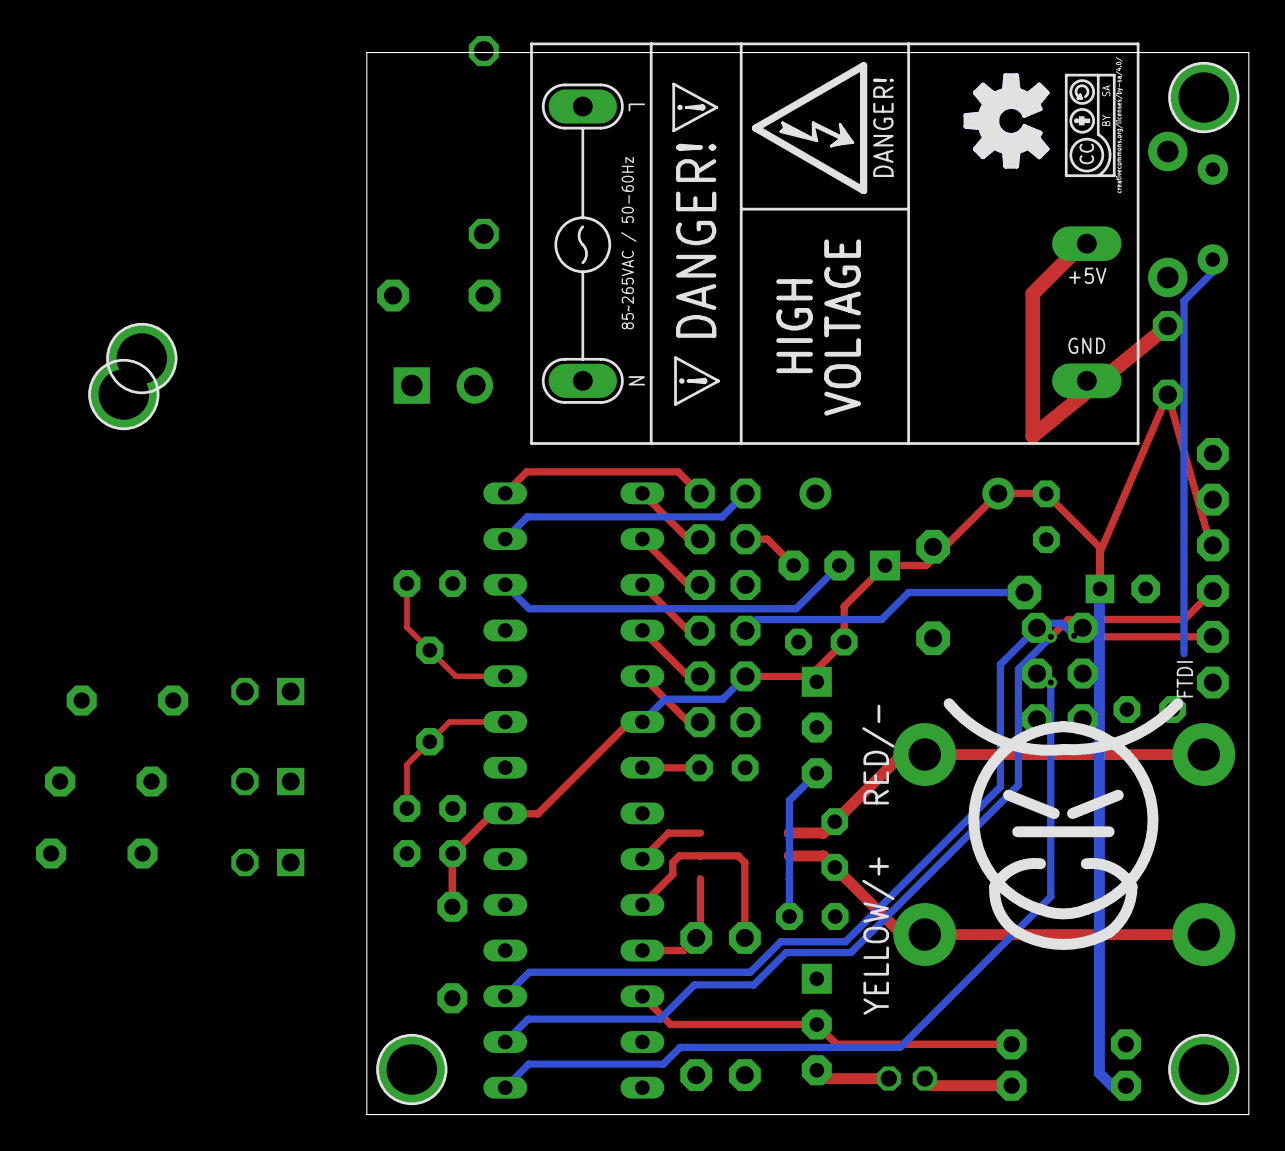
[picture p22: board pidplate-mk-2.brd from below]

Board: 2 copper layers, 49.0 x 59.0 mm, 50 parts (3 on the bottom side), 35 nets.

Other parts of the board:
U$1: COW
U$2: CC-BY-SA-4.0-NO-URL
U$3: CC-BY-SA-4.0-URL-BOTTOM
U$4: OSHWLOGO_BOT_0.2
